Kevinive/Mini_UPS/src/Include.h

#ifndef __INCLUDE_H
#define __INCLUDE_H

#include "UPS_Config.h"
#include "Arduino.h"
#include <avr/sleep.h>
#include <avr/power.h>
#include <avr/wdt.h>
#include <avr/pgmspace.h>
#include <Wire.h>
#include <EEPROM.h>
#include <SPI.h>
#include <DS3231.h>
#include "CodeTable.h"
#include "OLED.h"
#include "NRF24L01forArduino.h"
#include "WDTwake.h"


#endif
